cactorium/linear-sensors/capacitive-fw/filter/data/data_synced2.png

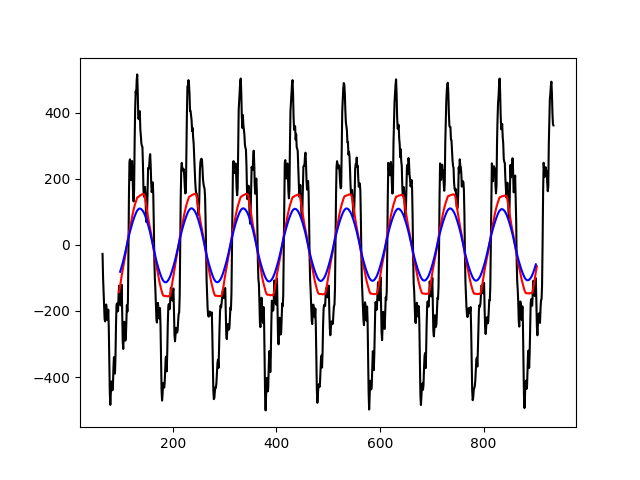
capacitive-fw/filter/data/data_synced2.png
