cactorium/linear-sensors/capacitive-fw/filter/data/data_synced2_0.png

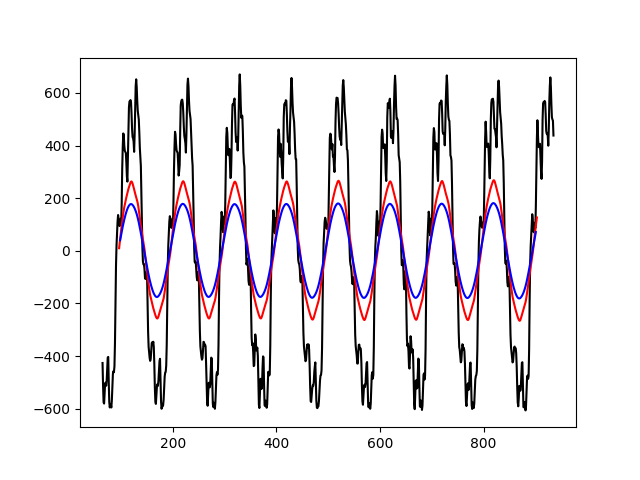
capacitive-fw/filter/data/data_synced2_0.png
