cactorium/linear-sensors/capacitive-fw/filter/data/data_synced3.png

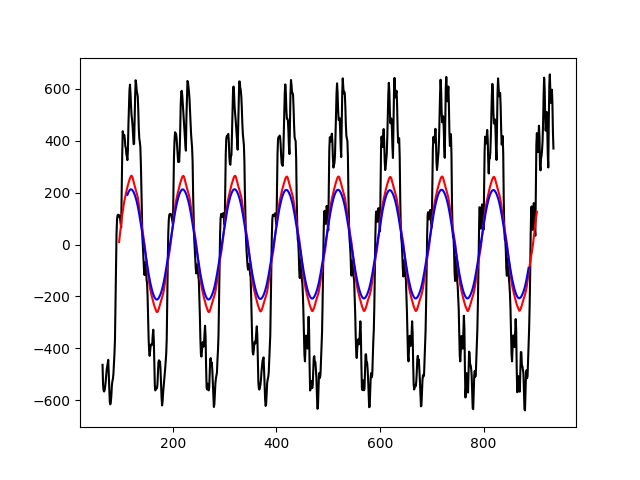
capacitive-fw/filter/data/data_synced3.png
