cactorium/linear-sensors/capacitive-fw/src/cordic_consts.h

#include <stdint.h>
#include <math.h>

const int64_t cordic_consts[32] = {
  0.7853981633974483*HALF_SCALE_PHASE_UNITS/M_PI,
  0.4636476090008061*HALF_SCALE_PHASE_UNITS/M_PI,
  0.24497866312686414*HALF_SCALE_PHASE_UNITS/M_PI,
  0.12435499454676144*HALF_SCALE_PHASE_UNITS/M_PI,
  0.06241880999595735*HALF_SCALE_PHASE_UNITS/M_PI,
  0.031239833430268277*HALF_SCALE_PHASE_UNITS/M_PI,
  0.015623728620476831*HALF_SCALE_PHASE_UNITS/M_PI,
  0.007812341060101111*HALF_SCALE_PHASE_UNITS/M_PI,
  0.0039062301319669718*HALF_SCALE_PHASE_UNITS/M_PI,
  0.0019531225164788188*HALF_SCALE_PHASE_UNITS/M_PI,
  0.0009765621895593195*HALF_SCALE_PHASE_UNITS/M_PI,
  0.0004882812111948983*HALF_SCALE_PHASE_UNITS/M_PI,
  0.00024414062014936177*HALF_SCALE_PHASE_UNITS/M_PI,
  0.00012207031189367021*HALF_SCALE_PHASE_UNITS/M_PI,
  6.103515617420877e-05*HALF_SCALE_PHASE_UNITS/M_PI,
  3.0517578115526096e-05*HALF_SCALE_PHASE_UNITS/M_PI,
  1.5258789061315762e-05*HALF_SCALE_PHASE_UNITS/M_PI,
  7.62939453110197e-06*HALF_SCALE_PHASE_UNITS/M_PI,
  3.814697265606496e-06*HALF_SCALE_PHASE_UNITS/M_PI,
  1.907348632810187e-06*HALF_SCALE_PHASE_UNITS/M_PI,
  9.536743164059608e-07*HALF_SCALE_PHASE_UNITS/M_PI,
  4.7683715820308884e-07*HALF_SCALE_PHASE_UNITS/M_PI,
  2.3841857910155797e-07*HALF_SCALE_PHASE_UNITS/M_PI,
  1.1920928955078068e-07*HALF_SCALE_PHASE_UNITS/M_PI,
  5.960464477539055e-08*HALF_SCALE_PHASE_UNITS/M_PI,
  2.9802322387695303e-08*HALF_SCALE_PHASE_UNITS/M_PI,
  1.4901161193847655e-08*HALF_SCALE_PHASE_UNITS/M_PI,
  7.450580596923828e-09*HALF_SCALE_PHASE_UNITS/M_PI,
  3.725290298461914e-09*HALF_SCALE_PHASE_UNITS/M_PI,
  1.862645149230957e-09*HALF_SCALE_PHASE_UNITS/M_PI,
  9.313225746154785e-10*HALF_SCALE_PHASE_UNITS/M_PI,
  4.656612873077393e-10*HALF_SCALE_PHASE_UNITS/M_PI,
};
