cactorium/linear-sensors/capacitive-fw/src/trig_consts.h

#define quadrant_size 24

const int32_t trig_quadrant[quadrant_size+1] = {
  0, 140452150, 280302863, 418953276, 555809666, 690285995, 821806412, 949807729, 1073741823, 1193077990, 1307305213, 1415934355, 1518500249, 1614563691, 1703713324, 1785567395, 1859775392, 1926019545, 1984016187, 2033516967, 2074309916, 2106220350, 2129111626, 2142885719, 2147483647
};
